tobychui/Weather-Pet-Display/src/res/backgrounds/afternoon.png

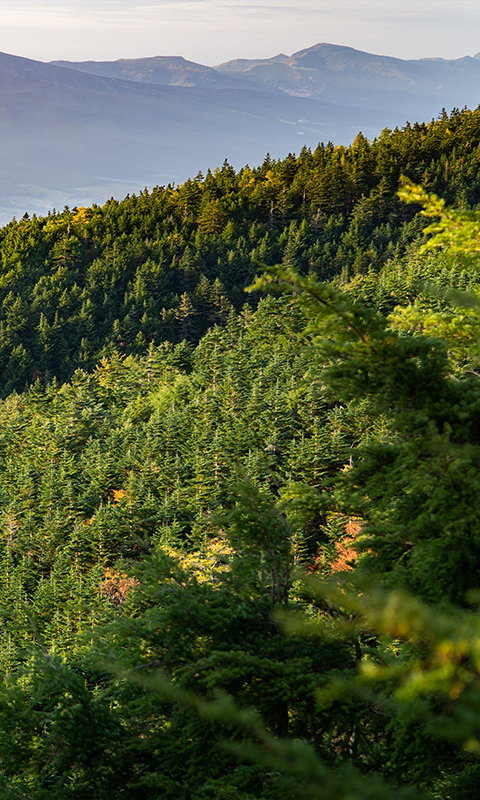
src/res/backgrounds/afternoon.png
