tobychui/Weather-Pet-Display/src/res/backgrounds/midnight.png

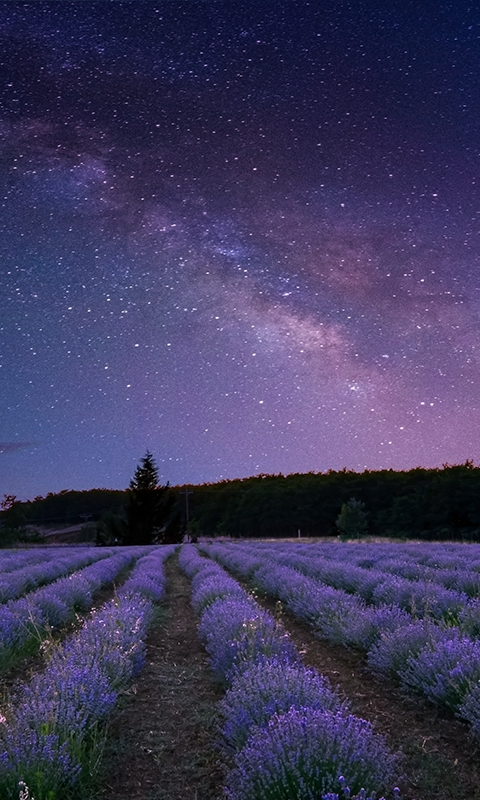
src/res/backgrounds/midnight.png
