tobychui/Weather-Pet-Display/src/res/backgrounds/morning.png

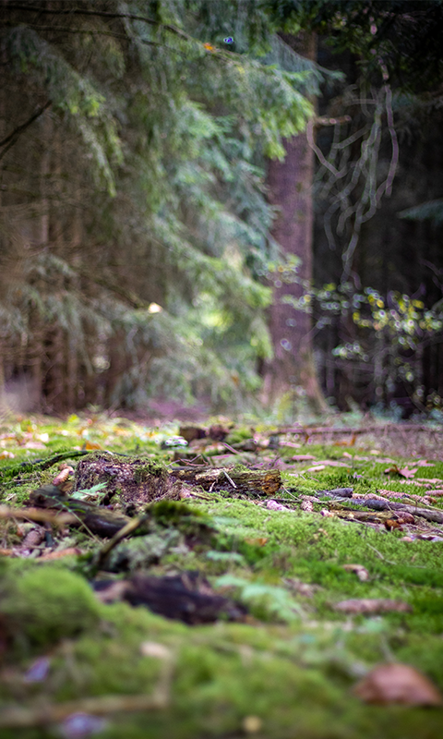
src/res/backgrounds/morning.png
