tobychui/Weather-Pet-Display/src/res/backgrounds/night.png

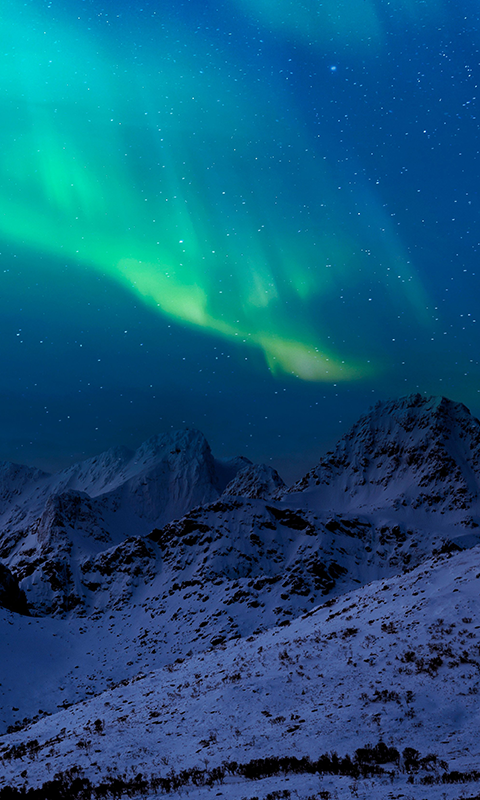
src/res/backgrounds/night.png
