tobychui/Weather-Pet-Display/src/res/backgrounds/noon.png

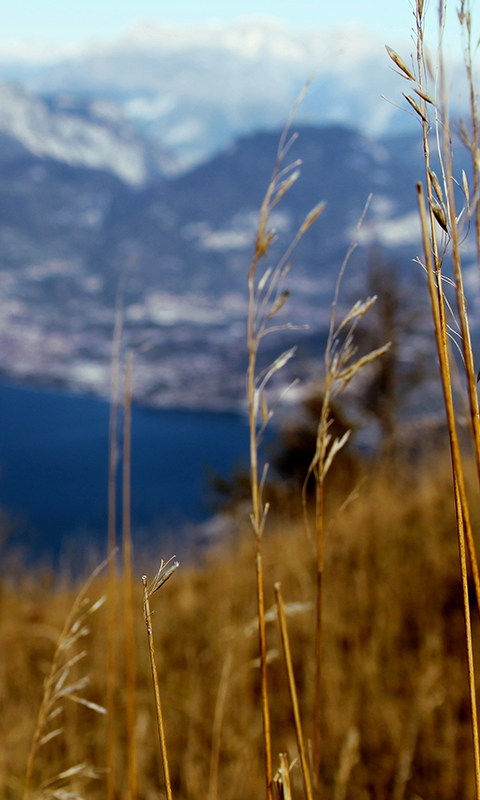
src/res/backgrounds/noon.png
