tobychui/Weather-Pet-Display/src/res/backgrounds/sunset.png

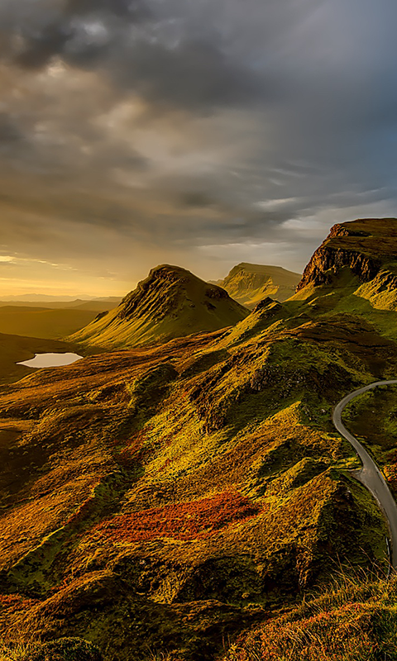
src/res/backgrounds/sunset.png
