tobychui/Weather-Pet-Display/src/res/dialog.png

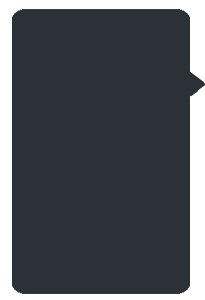
src/res/dialog.png
