tobychui/Weather-Pet-Display/src/res/ghost/blink2.png

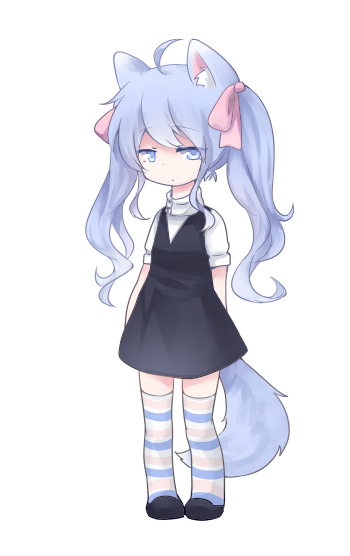
src/res/ghost/blink2.png
