tobychui/Weather-Pet-Display/src/res/ghost/menu_background.png

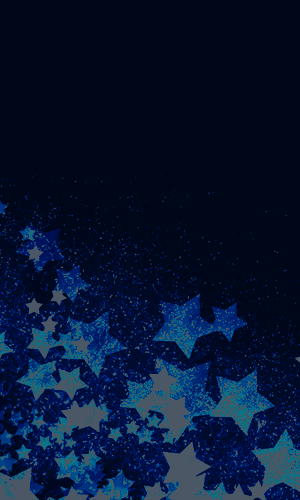
src/res/ghost/menu_background.png
