tobychui/Weather-Pet-Display/src/res/ghost/menu_foreground.png

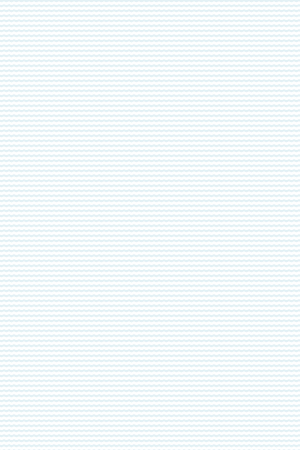
src/res/ghost/menu_foreground.png
