tobychui/Weather-Pet-Display/src/res/ghost/surface1.png

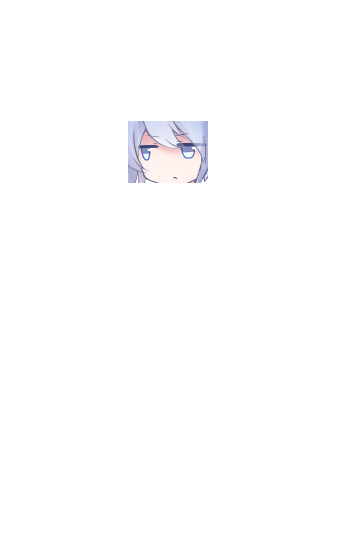
src/res/ghost/surface1.png
