tobychui/Weather-Pet-Display/src/res/ghost/surface1000.png

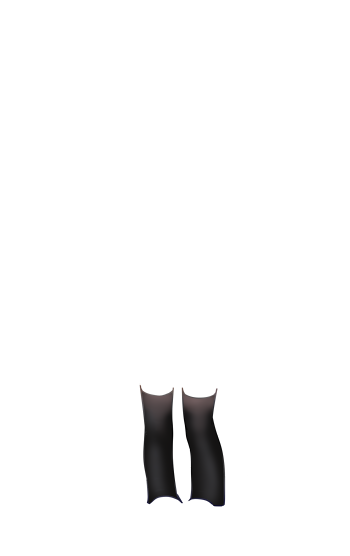
src/res/ghost/surface1000.png
