tobychui/Weather-Pet-Display/src/res/ghost/surface1353.png

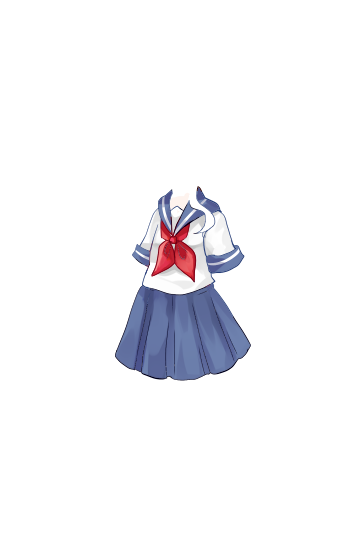
src/res/ghost/surface1353.png
