tobychui/Weather-Pet-Display/src/res/ghost/surface1400.png

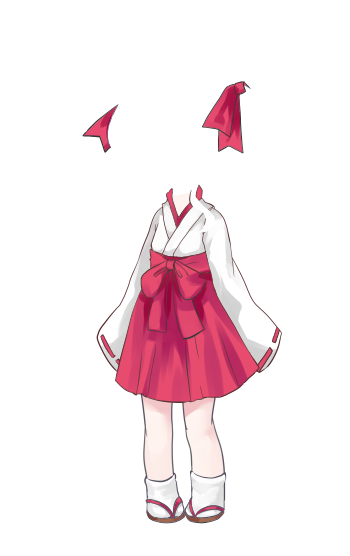
src/res/ghost/surface1400.png
